Shaurya-Ashu/RGB-AddOn-Files/Assembly/Screenshot 2026-03-03 at 3.33.58 PM.png

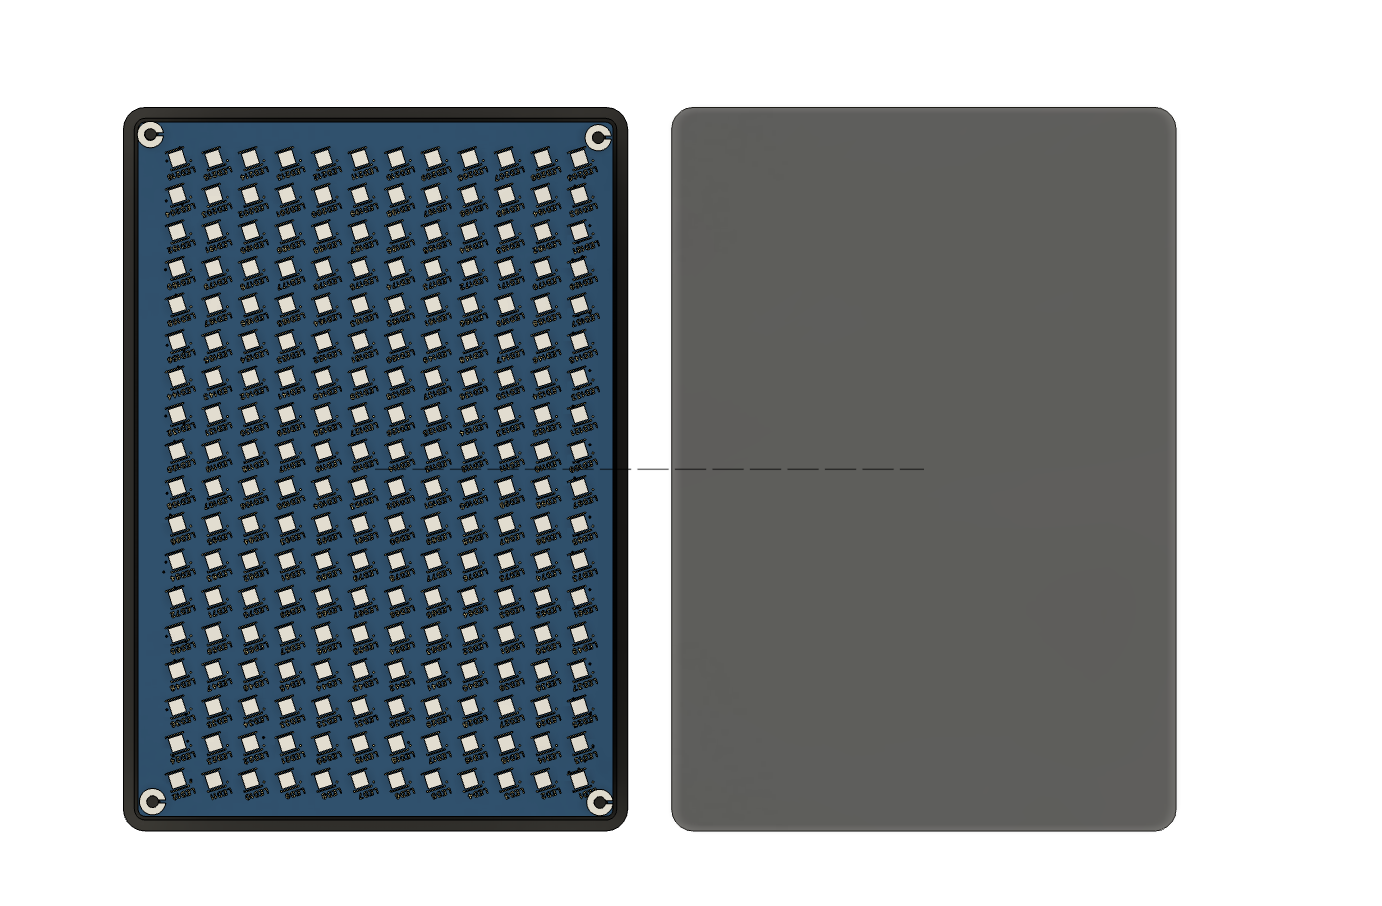
Assembly/Screenshot 2026-03-03 at 3.33.58 PM.png
